jb66dmg52h-dotcom/RoyalNode/docs/UNROUTED_SUMMARY_REV_A.md

# Unrouted Summary Rev A

Generated from `hardware/fabrication/RoyalNode_drc.rpt`.

This file is a layout planning aid, not a manufacturing release note. Counts are KiCad ratsnest-pair counts, so a net with several components can appear multiple times.

Total unrouted pairs: 0

| Net | Ratsnest pairs | Layout note |
|---|---:|---|
