jb66dmg52h-dotcom/RoyalNode/docs/U1_RIGHT_SIDE_REFACTOR_REV_A.md

# U1 Right-Side Refactor Rev A

This note captures the next charger-layout work package after the clean
11-unrouted checkpoint.

## Current Gate

```text
make layout-status
  ERC: 0
  DRC: 0 active violations/warnings; footprint-library mismatch is ignored by project policy for tracked local release-candidate footprints
  Unrouted: 5 ratsnest pairs
```

The DRC gate has 0 active violations/warnings. Footprint-library mismatch is
ignored by project policy for tracked local release-candidate footprints.

## Accepted State To Preserve

- `BQ_SW1` is routed from U1/C216 to L1 with a left-side wrap.
- `BQ_SYS` has an accepted entry via at 65.80, 71.80 mm.
- C216/`BQ_BTST1` is locally tied to U1 and the SW1 escape.
- C218/`BQ_SDRV` is now staged at 69.20, 71.20 mm, with a local top-layer
  SDRV trace from U1 pad 24. This keeps SDRV close to U1 while clearing more
  of the SW2/SYS escape lane than the earlier 67.20, 70.80 mm placement.
- R203/R204 provide local `BQ_PROG` and `BQ_INT` support at 70.5 mm x.
- R204's `3V3` feed now drops through a local via at 69.68, 72.80 mm and
  ties into the existing `In2.Cu` 3.3 V spine, leaving the top-side U1
  right corridor clearer for `BQ_SW2`, `BQ_BTST2` and C218/`BQ_SDRV` work.
- `BQ_REGN` from C215/R200 to U1 pin 5 is now routed with a left-side U1
  jog and B.Cu return path. Preserve this route unless the REGN/TS/BATP
  support-passive group is fully replanned.
- `BQ_REGN` ILIM_HIZ/U1 pin 17 is now tied to the pin-5 REGN escape with a
  short top-layer bridge. Preserve this bridge unless the REGN/TS/BATP support
  cluster is fully replanned.
- `BATP_KELVIN` is routed from U1 BATP to R202 with a low-current two-layer
  sense branch.
- `BQ_PMID` is routed from U1 to the PMID capacitor bus with a lower U1 fanout,
  B.Cu bridge and top-layer cap-bank entry.

## Blocked Nets In This Cluster

- `BQ_SW2`
- `BQ_BTST2`
- nearby `BQ_VBUS`, `USB_VBUS_RAW` and `SOLAR_PROTECTED` entries

## Exact Conflict Map

The relevant U1 pad centers are:

| Pad | Net | Center |
|---:|---|---|
| 16 | `BQ_TS` | 66.850, 76.600 |
| 17 | `BQ_REGN` | 66.850, 76.200 |
| 18 | `BATP_KELVIN` | 66.875, 75.800 |
| 19 | `BQ_BTST2` | 66.862, 75.400 |
| 20 | `BQ_PROG` | 66.900, 75.000 |
| 21 | `BQ_INT` | 66.900, 74.600 |
| 22 | `BAT_RAW` | 66.900, 74.200 |
| 23 | `BAT_RAW` | 66.900, 73.800 |
| 24 | `BQ_SDRV` | 66.862, 73.400 |
| 25 | `BQ_SYS` | 65.900, 73.300 |
| 26 | `BQ_SW2` | 65.450, 73.300 |

Nearby routed or placed blockers:

| Item | Net | Current role |
|---|---|---|
| C218 | `BQ_SDRV` | Shifted right after R204 3.3 V reroute; preserve its local SDRV trace |
| R203 | `BQ_PROG` | Blocks direct BTST2 top route |
| R204 | `BQ_INT` / `3V3` | Local 3.3 V via clears the previous upper right-side top trace |
| `BQ_TS` via | `BQ_TS` | Blocks lower BTST2 dogleg |
| Q3 left pads | selector nets | Block right-side SW2 drop toward L1 |

## Rejected Trials To Avoid

- Do not move only L1 upward; it collides with the accepted TPS61088 input-cap
  cluster and U1 support passives.
- Do not route SW2 straight down or through the U1 pad row.
- Do not shift the accepted SYS entry via rightward unless C218/SDRV is moved
  first.
- Do not route BTST2 directly through the R203/PROG corridor.
- A post-C218-move BTST2 dogleg trial still failed: the left pocket crowded
  `BQ_TS`/I2C_SDA, and the right pocket shorted into the accepted
  `BQ_PROG` local route. Move or reroute R203/`BQ_PROG` before retrying
  `BQ_BTST2`.
- A vertical R203 relocation at 72.8, 76.8 mm was rejected. The rotated pad
  order put the GND pad in the PROG feed path, added a solder-mask bridge and
  introduced an extra R203 footprint/library warning.
- Do not place a BTST2 via beside U1 pads 18-20; hole clearance and existing
  B.Cu/In1 corridors fail.
- Do not move C218 upward into the TPS61088/BQ_SYS input-cap area. A trial at
  69.2, 68.0 mm shorted `BQ_SDRV` into C401/`BQ_SYS`, overlapped C401's
  courtyard and starved C218's ground thermal.
- The C218 move to 69.2, 71.2 mm is now accepted after rerouting R204's
  3.3 V feed. Do not restore the earlier 67.2, 70.8 mm placement unless a
  later SW2/BTST2 pass proves it necessary.
- Do not route R204's 3.3 V feed on `In1.Cu` across x73.5 mm; that lane
  crosses the accepted `BQ_ACDRV1` route.
- 2026-07-28 BTST2 dogleg trials showed the tight top-layer lane between
  `BQ_TS` and `BQ_PROG` is too narrow at the current 0.15 mm minimum trace
  width. A dogleg at x68.50 mm cleared `BQ_PROG` but missed `BQ_TS` clearance
  by 0.025 mm; shifting right cleared `BQ_TS` but crowded `BQ_PROG`.
- Do not solve that miss by dropping the BTST2 track to 0.10 mm. KiCad rejects
  that under the Rev A 0.15 mm board minimum.
- Moving the `BQ_TS` via left to open the BTST2 lane was rejected because it
  collided with the accepted `I2C_SDA` and `BQ_REGN` escape region.
- Bending the `BQ_PROG` route below BTST2 was rejected because it crowded the
  accepted `BQ_INT` top-layer route. `BQ_PROG` and `BQ_INT` must be moved as a
  pair if this lane is opened.
- Moving C217 into the immediate U1 pin field was rejected. The capacitor
  overlapped/crowded `BAT_RAW`, `BATP_KELVIN`, `BQ_SDRV`, `BQ_PROG`, `BQ_INT`,
  R203/R204 and the Q3 selector corridor.
- A via-based BTST2 escape from U1 to C217 was rejected because the U1-side via
  crowded `BQ_PROG`, `BAT_RAW` and `BATP_KELVIN`, and the back-layer route
  crossed the accepted `BATP_KELVIN` sense branch.

## Refactor Goal

Create a legal right-side escape corridor where:

1. `BQ_SYS` keeps a short, quiet U1 entry.
2. `BQ_SW2` leaves U1 without crossing SDRV, SYS, 3.3 V, Q3 or I2C.
3. `BQ_BTST2` stays close to C217 and avoids PROG/TS.
4. `BATP_KELVIN` remains a routed sense connection, not part of high-current BAT copper.
5. Q3 selector pads remain serviceable and do not mask-bridge to switch-node copper.

## Candidate Placement Strategy

Try as a grouped pass only:

- Keep R203/`BQ_PROG` clear of the BTST2 path or move it below/right as part of
  the same pass.
- Re-evaluate whether C217 should stay at 72.8, 82.0 mm or rotate/shift after
  SW2 has a legal exit.
- Do not move Q3 casually; if Q3 moves, update the input-selector route group
  and check XT30 connector clearance.

## Acceptance Test

Before accepting the pass:

```text
make generate-board
make layout-status
```

The pass is accepted only if:

- unconnected count decreases below 17, or a documented placement improvement is
  achieved without increasing it;
- ERC remains 0;
- DRC remains at 0 active violations/warnings;
- no test points, shunts or measurement links are added.
