jb66dmg52h-dotcom/RoyalNode/docs/POWER_INPUT_DECISIONS.md

# 2Watt Project Power Input Decisions

## Issue 1: BQ25798 dual-input source mux

**Status: LOCKED**

Use the full BQ25798 dual-source mux topology:

```text
Solar source -> back-to-back ACFET/RBFET pair -> common VBUS
USB source   -> back-to-back ACFET/RBFET pair -> common VBUS
```

Requirements:

- Solar source is assigned to VAC1 control/sense.
- USB source is assigned to VAC2 control/sense.
- Each source receives its own back-to-back N-channel MOSFET pair.
- The BQ25798 controls the source-selection FETs through its source-driver outputs.
- No source may backfeed the other source or its connector.

This supersedes all earlier one-pair or direct-source concepts.

## Issue 2: Solar overvoltage and reverse-polarity protection

**Status: LOCKED**

Use an active input-protection stage based on:

- Controller: Analog Devices LTC4365ITS8-1#TRMPBF
- Package: TSOT-23-8
- Temperature range: -40 C to +85 C
- External protection devices: one back-to-back N-channel MOSFET pair

Locked solar path:

```text
Solar XT30
  -> 5 A-class fuse
  -> LTC4365-1 protection controller
  -> back-to-back N-channel protection MOSFETs
  -> BQ25798 solar-source ACFET/RBFET mux pair
  -> common BQ25798 VBUS
```

Locked threshold targets:

- Undervoltage cutoff: approximately 4.5 V for the current 6 V solar-panel class
- Overvoltage cutoff: approximately 25 V

Requirements:

- The LTC4365 protection pair handles reverse polarity and disconnects the panel during excessive input voltage.
- The BQ25798 mux pair remains a separate stage for source selection and source-to-source reverse blocking.
- The previously selected SMBJ22A TVS is removed from the locked BOM.
- The previously selected BSL303SPE P-channel reverse-polarity MOSFET is removed from the locked BOM.
- Recommended panel cold-weather Voc must remain below the 25 V cutoff target with suitable tolerance margin.
- The fuse and wiring must support the selected 6 V / 20 W panel's maximum-power current and short-circuit current.

## Issue 3: Shared USB-C charging-current policy

**Status: LOCKED**

The XIAO USB-C connector remains shared between firmware/data operation and BQ25798 main-battery charging.

Locked policy:

- Initial BQ25798 USB input-current limit: 100 mA.
- After successful USB enumeration by the XIAO: raise the BQ25798 USB input-current limit to 350 mA.
- Never exceed 350 mA through the shared XIAO USB-C charging branch.
- BQ25798 D+ and D- remain unconnected.
- Solar remains the primary high-power charging source.

Firmware requirement:

- Initialize the BQ25798 USB path at 100 mA.
- Raise to 350 mA only after the USB stack confirms successful enumeration.
- Fall back to 100 mA after disconnect, USB reset or enumeration failure.

## Issue 4: LM66100 exact wiring

**Status: LOCKED**

Use LM66100DCKR as the always-enabled ideal-diode feed from the protected 1S battery/system node to the XIAO underside BAT input.

Locked path:

```text
Protected battery/system node
  -> LM66100 VIN
  -> LM66100 VOUT
  -> 2-pin JST-GH positive
  -> XIAO BAT pad

Common GND
  -> 2-pin JST-GH ground
  -> XIAO GND
```

Pin and support-component requirements:

- VIN: protected battery/system node.
- VOUT: JST positive output to XIAO BAT.
- GND: common system ground.
- CE: tie high to VIN for always-enabled operation.
- ST: leave unconnected.
- Input bypass capacitor: 1 uF ceramic located close to VIN/GND.
- Output bypass capacitor: 1 uF ceramic located close to VOUT/GND.
- No MCU GPIO control is required.

Functional intent:

- XIAO automatically receives battery power whenever the main protected battery is present.
- Reverse current from the XIAO side toward the main battery rail is blocked by the ideal-diode path.
- XIAO remains socketed and USB-C remains available for firmware/data operation.

## Issue 5: BQ25798 BATP Kelvin routing

**Status: LOCKED**

Locked connection:

```text
Battery XT30 positive pad
  -> dedicated Kelvin sense trace
  -> 100 ohm series resistor
  -> BQ25798 BATP
```

Routing and component requirements:

- BATP sense origin is the battery XT30 positive pad itself.
- Do not sense BATP from the BQ25798 BAT power pin, from the charger-side BAT copper, or from an intermediate high-current node.
- Use a dedicated low-current sense trace from the battery connector pad to BATP.
- The BATP sense trace must not carry battery charge or system current.
- Route the BATP trace away from SW1, SW2 and other noisy switching nodes.
- Place the 100 ohm series resistor close to the BQ25798 BATP pin.
- Do not add a BATP capacitor unless explicitly required by TI guidance used during final schematic verification.
- Keep BATP sensing tied to the actual battery-positive terminal side of any future switching element.

Functional intent:

- The charger measures actual battery-terminal voltage rather than voltage elevated by IR drop in the high-current charge path.
- The Kelvin connection protects charge-voltage accuracy, especially at the 2 A charge target.

## Issue 6: External MOSFET selection and LTC4365 threshold divider

**Status: LOCKED**

### Common MOSFET device

Use one common dual N-channel 40 V MOSFET device for all three back-to-back pairs:

- Manufacturer: Infineon
- Device: ISA170170N04LMDS
- Ordering code: ISA170170N04LMDSXTMA1
- Configuration: dual N-channel
- VDS rating: 40 V
- Package: SO-8 / PG-DSO-8
- Logic-level device
- RDS(on) max at VGS = 4.5 V: 23.6 milliohm per MOSFET
- QG typ at 4.5 V: 6 nC

Use one dual-MOSFET package for each function:

1. One ISA170170N04LMDS package for the LTC4365 solar protection pair.
2. One ISA170170N04LMDS package for the BQ25798 solar ACFET/RBFET pair.
3. One ISA170170N04LMDS package for the BQ25798 USB ACFET/RBFET pair.

### LTC4365 UV/OV divider

```text
VIN
 |
 R3 = 1.78 MOhm
 |
 UV
 |
 R2 = 180 kOhm
 |
 OV
 |
 R1 = 40.2 kOhm
 |
GND
```

Nominal thresholds:

- UV falling cutoff: approximately 4.54 V nominal
- UV rising/reconnect: final value to be checked against LTC4365 hysteresis and selected panel behavior
- OV rising cutoff: approximately 24.9 V nominal
- OV falling/reconnect: final value to be checked against LTC4365 hysteresis

## Issue 7: BQ25798 TS policy for Rev A

**Status: LOCKED**

Rev A uses a real battery-mounted NTC. The earlier fixed simulated-temperature TS concept is superseded.

Design intent:

- Fit a 2-pin JST-GH battery NTC connector.
- Use a Semitec 103AT-2 10 kOhm NTC mounted to the battery pack.
- Use the locked 5.23 kOhm REGN-to-TS and 30.1 kOhm TS-to-NTC-node network.
- Do not add a TS bypass jumper or simulated-temperature bench network.

## Issue 8: BQ25798 remaining static/configuration pins

**Status: LOCKED**

Locked pin-audit decisions:

- CE: tie directly to GND so charging is hardware-enabled; firmware retains charge control through EN_CHG.
- ILIM_HIZ: tie to REGN so the hardware pin permits maximum input current; actual USB and solar current limits are managed through I2C.
- INT: add a 10 kOhm pull-up to the XIAO 3.3 V logic rail, but do not route INT to the XIAO in Rev A.
- SDRV: no ship FET is used; fit 1 nF, 50 V ceramic from SDRV to GND.
- PROG: 4.7 kOhm to GND for 1S / 750 kHz configuration.
- D+ and D-: no connect.
- QON: leave unconnected; use the internal pull-up.
- SCL/SDA: connect to XIAO I2C with 10 kOhm pull-ups to 3.3 V.
- BATP: retain the previously locked 100 ohm Kelvin-sense connection to battery XT30 positive.

Power-stage support components to follow TI reference values during schematic capture:

- BTST1 to SW1: 47 nF ceramic, at least 10 V.
- BTST2 to SW2: 47 nF ceramic, at least 10 V.
- REGN: 4.7 uF ceramic, at least 10 V, close to the pin.
- VBUS: local 2 x 10 uF plus 0.1 uF ceramic decoupling.
- BAT: local 2 x 10 uF ceramic decoupling.
- SYS: local 5 x 10 uF plus 0.1 uF ceramic decoupling.
- PMID: local 3 x 10 uF plus 0.1 uF ceramic decoupling.
- GND / exposed thermal pad: solid low-impedance ground connection with thermal vias.

## Issue 9: STAT LED final implementation

**Status: LOCKED**

Use a buffered active-low STAT indicator so the BQ25798 STAT node keeps its recommended 10 kOhm pull-up and the LED current does not load the STAT pin directly.

Locked circuit:

```text
3.3 V ---- 10 kOhm ----+---- BQ25798 STAT
                       |
                       +---- gate of BSS84 P-channel MOSFET

BSS84 source -> 3.3 V
BSS84 drain  -> LED anode
LED cathode  -> 2.2 kOhm -> GND
```

Behavior:

- STAT released/high: BSS84 gate rises to 3.3 V, MOSFET off, LED off.
- STAT asserted/low during charging: BSS84 VGS becomes negative, MOSFET on, LED on.
- The STAT pin itself only sinks current through the 10 kOhm pull-up and MOSFET gate leakage, preserving the intended open-drain loading.

Parts:

- QSTAT: BSS84, SOT-23 P-channel MOSFET.
- RSTAT: 10 kOhm pull-up to XIAO 3.3 V rail.
- RLED: 2.2 kOhm.
- LED: low-current green or amber indicator, 0603 preferred.

## Issue 10: TPS61088 5 V radio-rail schematic closure

**Status: NEXT**

Next, finalize the TPS61088 support network for the dedicated 5 V / 2 A E22 radio rail: feedback divider, switching frequency resistor, current-limit resistor, compensation, EN treatment, input/output capacitance, and final inductor suitability.
